lucadaloia/MSP430-LDR_ECE492/MSP430 C Firmware/ProjectMaster.h

/*
 * ProjectMaster.h
 *
 *  Created on: May 5, 2026
 *      Author: Luca
 */

#ifndef PROJECTMASTER_H_
#define PROJECTMASTER_H_

#include <msp430.h>
#include "globals.h"
#include "ports.h"
#include "timers.h"
#include "ADC.h"



#endif /* PROJECTMASTER_H_ */
