lucadaloia/MSP430-LDR_ECE492/MSP430 C Firmware/globals.h

/*
 * globals.h
 *
 *  Created on: May 5, 2026
 *      Author: Luca
 */

#ifndef GLOBALS_H_
#define GLOBALS_H_

extern volatile int mode;
extern int ADC_Channel;
extern volatile int photo_val;
extern volatile int thumb_val;
extern volatile int initial_photo_val;


#endif /* GLOBALS_H_ */
